Data-Gator/Hardware/Board_Assembly_Guides/images/enclosure/laying_down_ortho.jpg

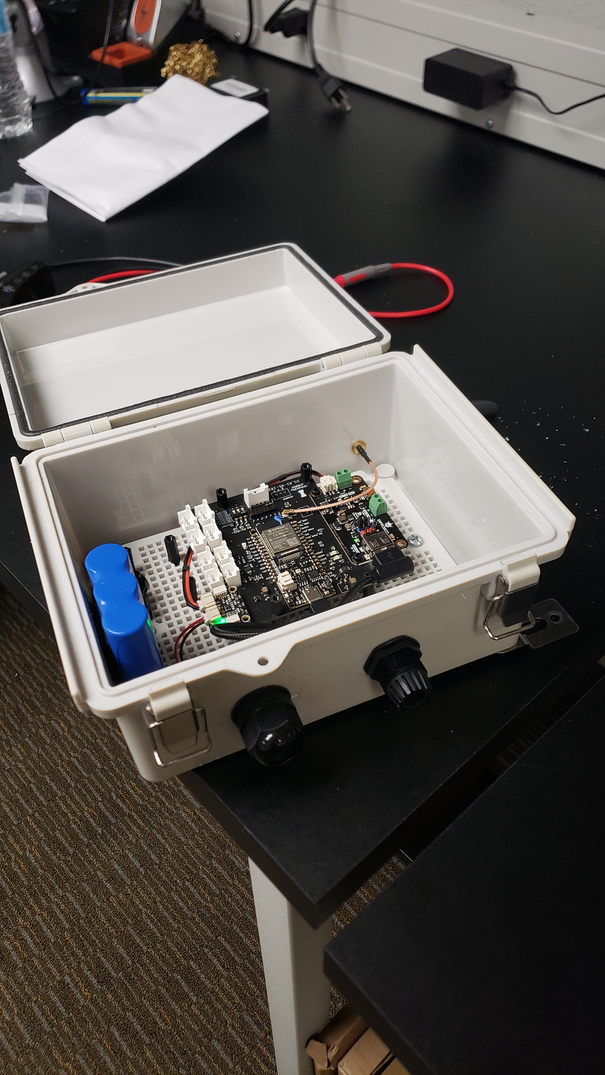
Board_Assembly_Guides/images/enclosure/laying_down_ortho.jpg
