Data-Gator/Hardware/Board_Assembly_Guides/images/firebeetle.jpg

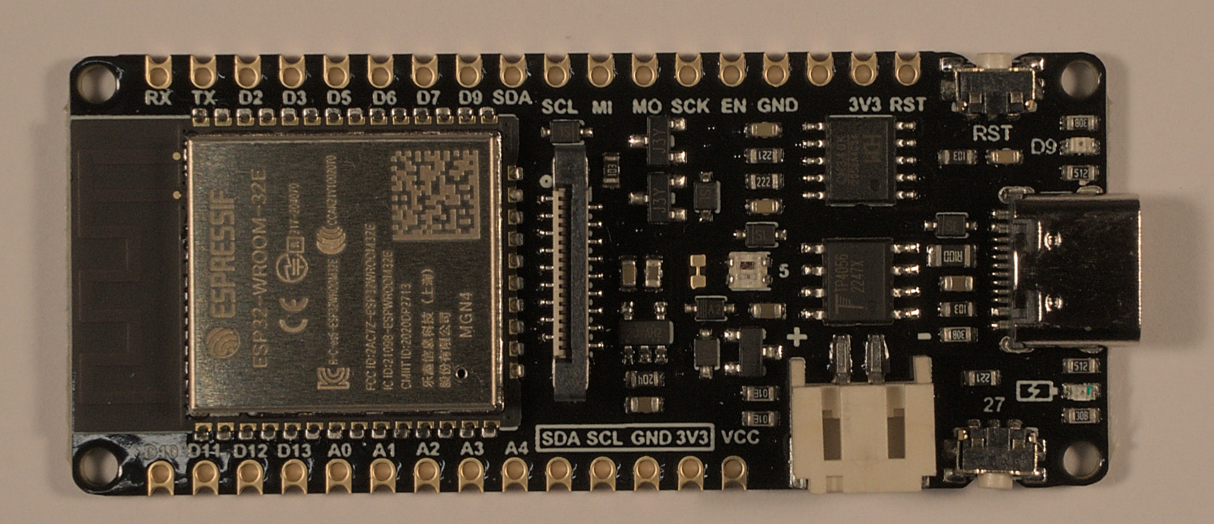
Board_Assembly_Guides/images/firebeetle.jpg
