Data-Gator/Hardware/Board_Assembly_Guides/images/switch.jpg

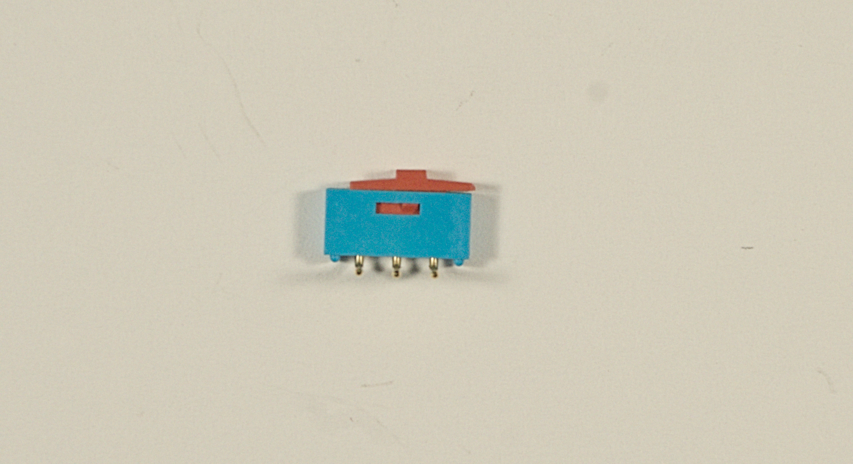
Board_Assembly_Guides/images/switch.jpg
